smilg/3ddie/silkscreen_images/3D GESTURE CONTROL.png

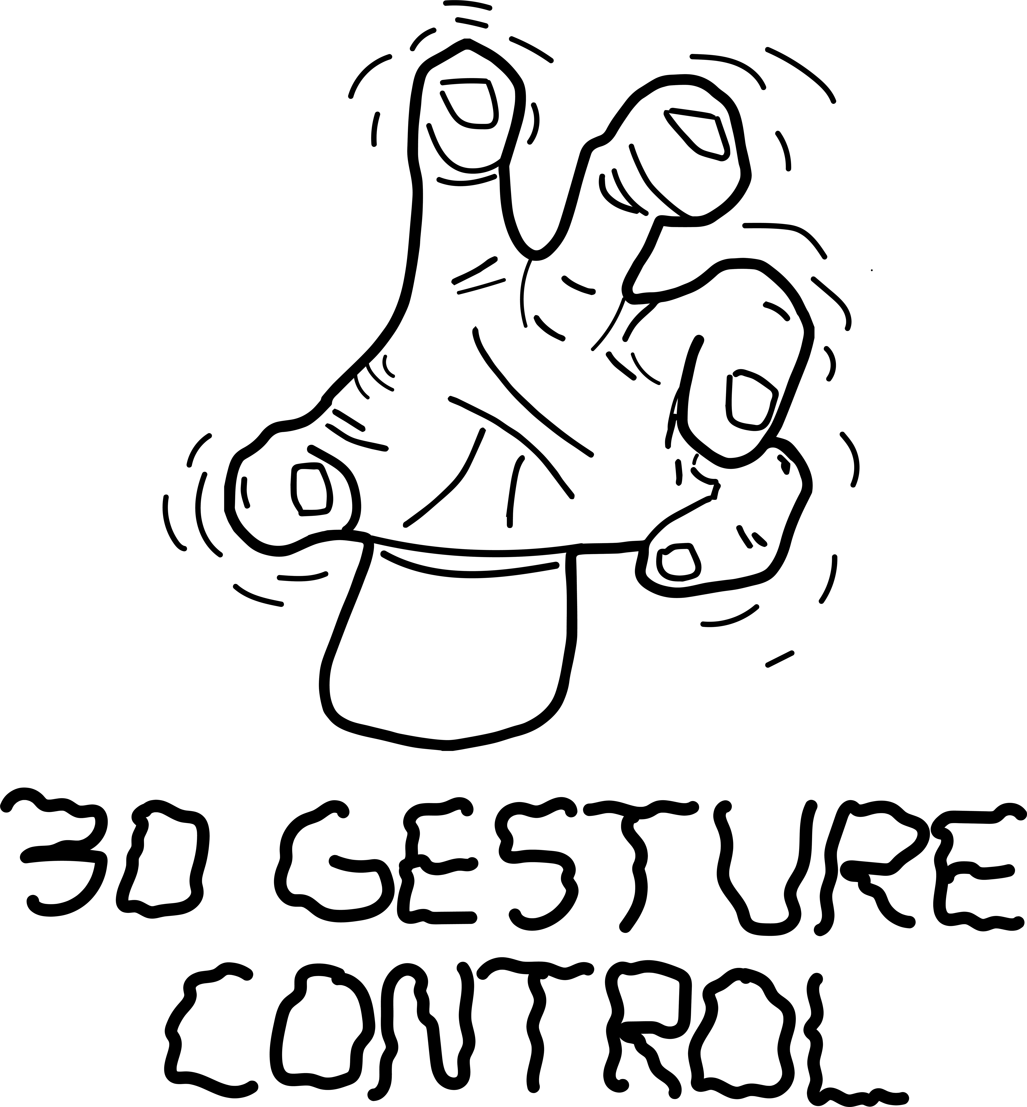
silkscreen_images/3D GESTURE CONTROL.png
