smilg/3ddie/3ddie/Eclectronics/3dshapes/CUI_SDS-50J.step

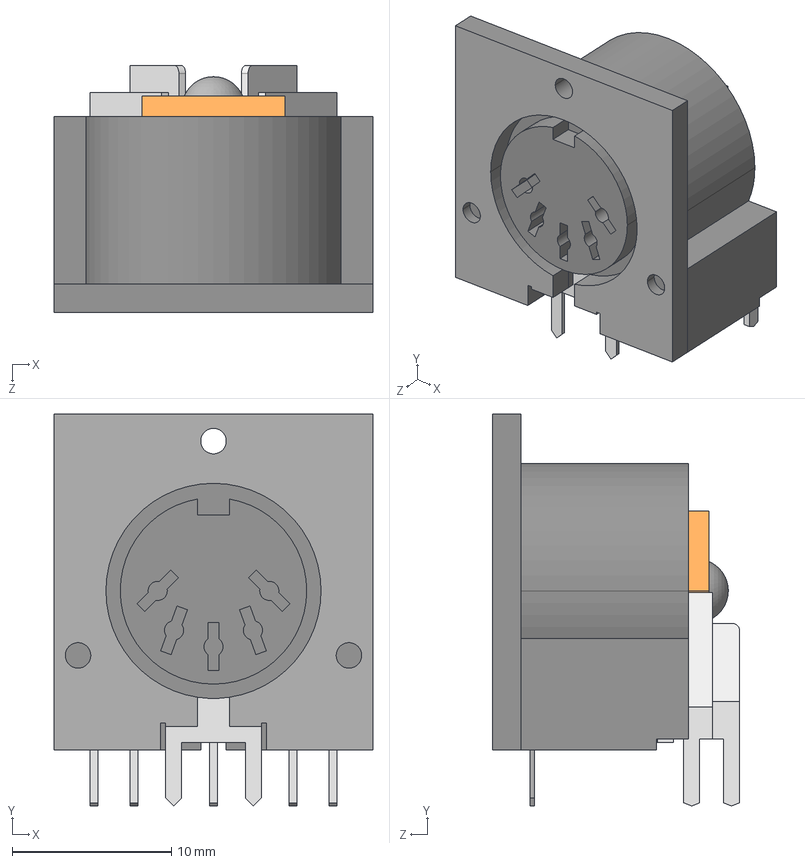
[picture p22: CAD file, 2022-10-23]
3ddie/Eclectronics/3dshapes/CUI_SDS-50J.step
20.0 x 24.6 x 15.5 mm
