smilg/3ddie/3ddie/Eclectronics/3dshapes/ABM10.STP

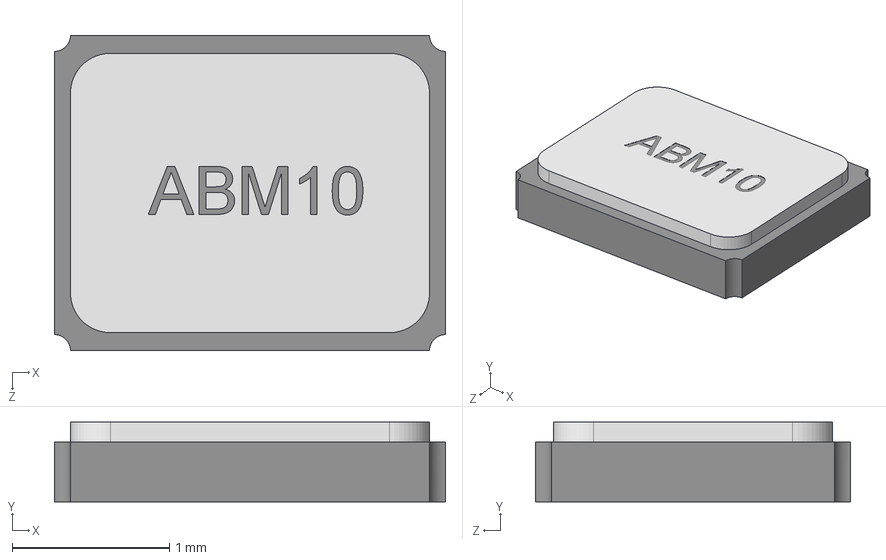
[picture p23: CAD file, 2022-10-23]
3ddie/Eclectronics/3dshapes/ABM10.STP
2.49 x 0.508 x 2.01 mm
