smilg/3ddie/3ddie/Eclectronics/3dshapes/RNR0011A.stp

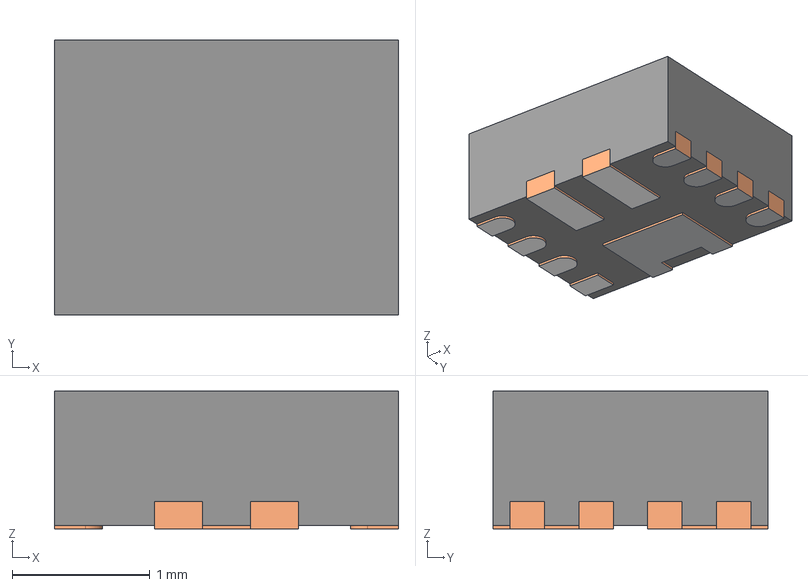
[picture p24: CAD file, 2022-10-23]
3ddie/Eclectronics/3dshapes/RNR0011A.stp
2.50 x 2.00 x 1.00 mm
FRAME-RNR0011A
BODY-QFN
PIN1-ID
