smilg/3ddie/3ddie/Eclectronics/3dshapes/CSTNE.step

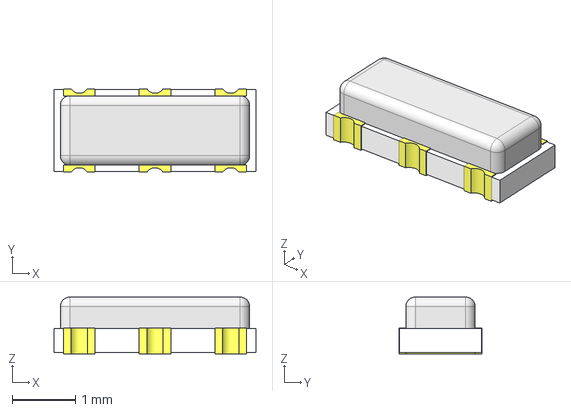
[picture p25: CAD file, 2022-10-23]
3ddie/Eclectronics/3dshapes/CSTNE.step
3.20 x 1.32 x 0.9 mm
