smilg/3ddie/3ddie/Eclectronics/3dshapes/QFN-32_5x5.stp

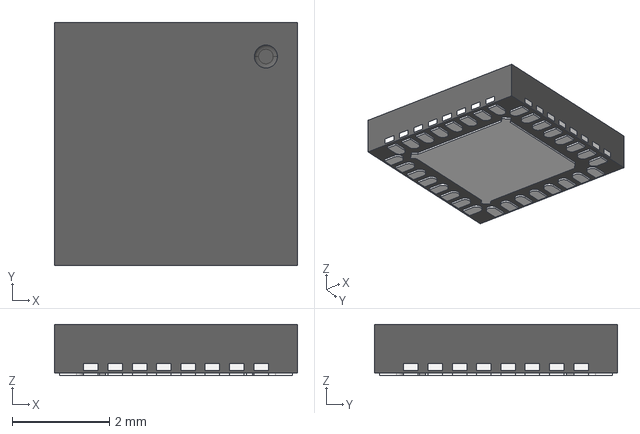
[picture p26: CAD file, 2022-10-23]
3ddie/Eclectronics/3dshapes/QFN-32_5x5.stp
5.00 x 5.00 x 1.05 mm
