smilg/3ddie/3ddie/Eclectronics/3dshapes/S4B-PH-SM4-TB.stp

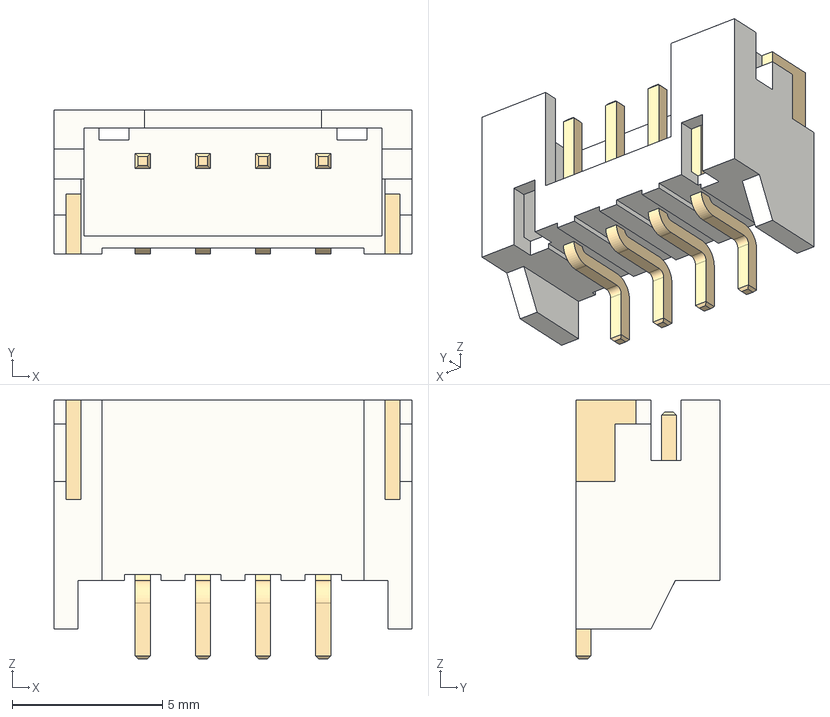
[picture p27: CAD file, 2022-10-23]
3ddie/Eclectronics/3dshapes/S4B-PH-SM4-TB.stp
11.9 x 4.80 x 8.60 mm
