smilg/3ddie/3ddie/Eclectronics/3dshapes/UFQFPN48.stp

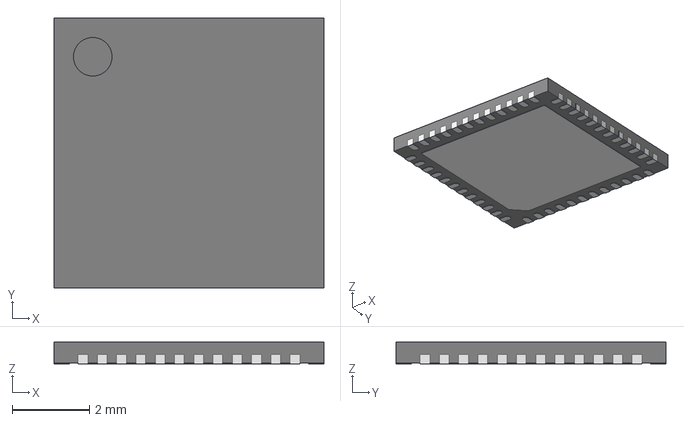
[picture p28: CAD file, 2022-10-23]
3ddie/Eclectronics/3dshapes/UFQFPN48.stp
7.00 x 7.00 x 0.57 mm
