smilg/3ddie/3ddie/Eclectronics/3dshapes/DFN-8-3x3-0_5.STEP

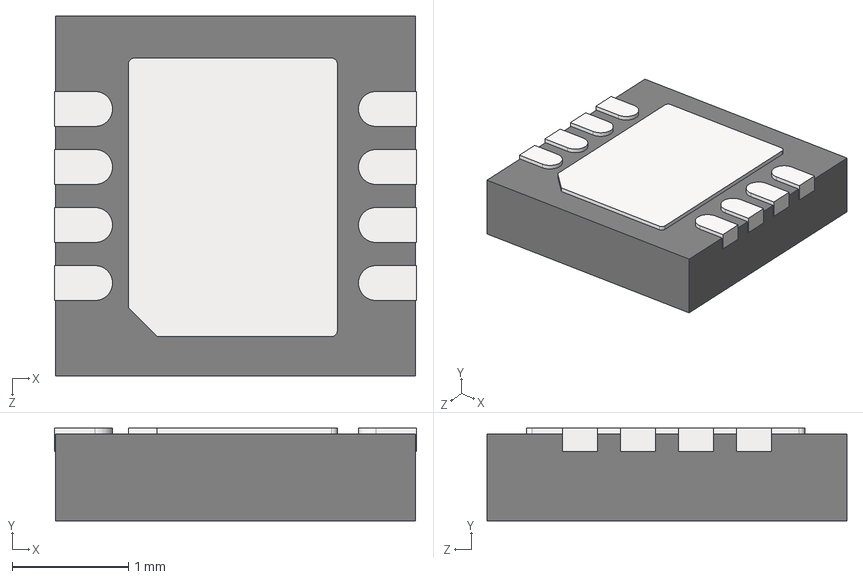
[picture p29: CAD file, 2022-10-23]
3ddie/Eclectronics/3dshapes/DFN-8-3x3-0_5.STEP
3.12 x 0.8 x 3.10 mm
User Library-My-DFN-8-3x3-0.5_Part 11
User Library-My-DFN-8-3x3-0.5_Body
User Library-My-DFN-8-3x3-0.5_14
User Library-My-DFN-8-3x3-0.5_13
User Library-My-DFN-8-3x3-0.5_2
User Library-My-DFN-8-3x3-0.5_1
User Library-My-DFN-8-3x3-0.5_11
User Library-My-DFN-8-3x3-0.5_3
User Library-My-DFN-8-3x3-0.5_12
User Library-My-DFN-8-3x3-0.5_4
User Library-My-DFN-8-3x3-0.5_TP
