smilg/3ddie/3ddie/Eclectronics/3dshapes/DFN8_3x3_0.65.step

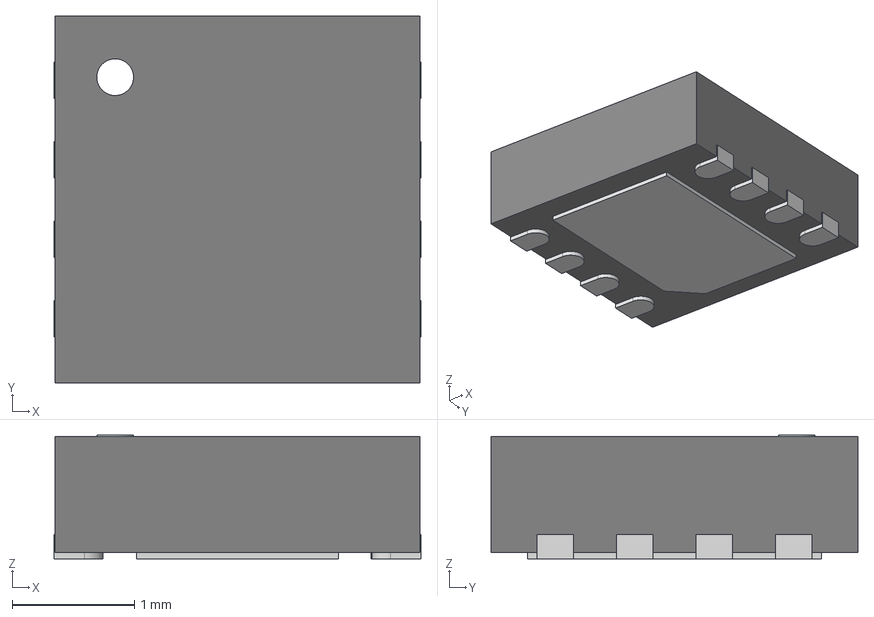
[picture p30: CAD file, 2022-10-23]
3ddie/Eclectronics/3dshapes/DFN8_3x3_0.65.step
3.00 x 3.00 x 1.01 mm
