smilg/3ddie/3ddie/Eclectronics/3dshapes/PA5003.182NLT.step

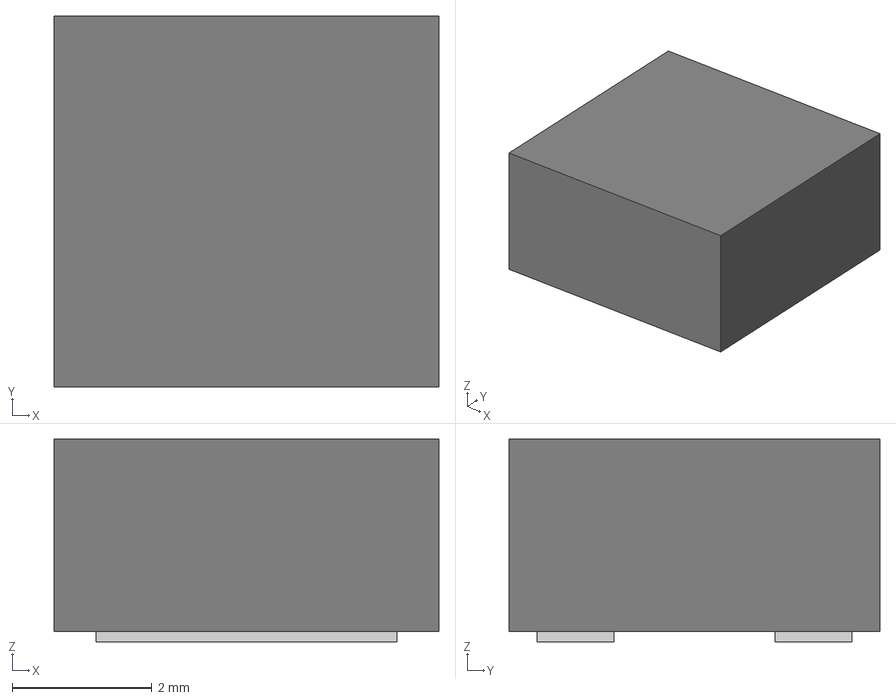
[picture p31: CAD file, 2022-10-23]
3ddie/Eclectronics/3dshapes/PA5003.182NLT.step
5.50 x 5.30 x 2.90 mm
